manomono-23/e-otomo/firmware/e-otomo/qr_pattern.h

#ifndef QR_PATTERN_H
#define QR_PATTERN_H

// QR code pattern data (33x33 bits packed into bytes)
// Generated for "https://e-otomo.manomono.net/"
const uint8_t qr_pattern[] = {
  0x00, 0x00, 0x00, 0x00, 0x00, // Row  0: 000000000000000000000000000000000
  0x00, 0x00, 0x00, 0x00, 0x00, // Row  1: 000000000000000000000000000000000
  0x3F, 0xA1, 0xB8, 0xFE, 0x00, // Row  2: 001111111010000110111000111111100
  0x20, 0xA7, 0xD4, 0x82, 0x00, // Row  3: 001000001010011111010100100000100
  0x2E, 0xB2, 0x96, 0xBA, 0x00, // Row  4: 001011101011001010010110101110100
  0x2E, 0xBA, 0x0C, 0xBA, 0x00, // Row  5: 001011101011101000001100101110100
  0x2E, 0x9A, 0x18, 0xBA, 0x00, // Row  6: 001011101001101000011000101110100
  0x20, 0xB8, 0x34, 0x82, 0x00, // Row  7: 001000001011100000110100100000100
  0x3F, 0xAA, 0xAA, 0xFE, 0x00, // Row  8: 001111111010101010101010111111100
  0x00, 0x0D, 0x7A, 0x00, 0x00, // Row  9: 000000000000110101111010000000000
  0x33, 0x8B, 0x1A, 0x5E, 0x00, // Row 10: 001100111000101100011010010111100
  0x2A, 0x41, 0xB8, 0xFE, 0x00, // Row 11: 001010100100000110111000111111100
  0x20, 0xB8, 0x2A, 0x42, 0x00, // Row 12: 001000001011100000101010010000100
  0x1A, 0x72, 0x96, 0x16, 0x00, // Row 13: 000110100111001010010110000101100
  0x2F, 0xE5, 0xF3, 0x44, 0x00, // Row 14: 001011111110010111110011010001000
  0x23, 0x6A, 0x18, 0xFE, 0x00, // Row 15: 001000110110101000011000111111100
  0x0B, 0x8F, 0xC8, 0x3A, 0x00, // Row 16: 000010111000111111001000001110100
  0x3F, 0x3D, 0x76, 0xA6, 0x00, // Row 17: 001111110011110101110110101001100
  0x3E, 0xD3, 0x13, 0x04, 0x00, // Row 18: 001111101101001100010011000001000
  0x28, 0x29, 0xA8, 0xF6, 0x00, // Row 19: 001010000010100110101000111101100
  0x09, 0x88, 0x3A, 0x0A, 0x00, // Row 20: 000010011000100000111010000010100
  0x06, 0x1A, 0x98, 0x26, 0x00, // Row 21: 000001100001101010011000001001100
  0x3E, 0xFD, 0xF7, 0xF2, 0x00, // Row 22: 001111101111110111110111111100100
  0x00, 0x32, 0x06, 0x22, 0x00, // Row 23: 000000000011001000000110001000100
  0x3F, 0x8F, 0xDE, 0xBA, 0x00, // Row 24: 001111111000111111011110101110100
  0x20, 0xB5, 0x76, 0x22, 0x00, // Row 25: 001000001011010101110110001000100
  0x2E, 0xB3, 0x1F, 0xF6, 0x00, // Row 26: 001011101011001100011111111101100
  0x2E, 0x89, 0xBA, 0x04, 0x00, // Row 27: 001011101000100110111010000001000
  0x2E, 0x88, 0x2F, 0x5E, 0x00, // Row 28: 001011101000100000101111010111100
  0x20, 0xA2, 0x9A, 0x16, 0x00, // Row 29: 001000001010001010011010000101100
  0x3F, 0xB5, 0xCA, 0xF4, 0x00, // Row 30: 001111111011010111001010111101000
  0x00, 0x00, 0x00, 0x00, 0x00, // Row 31: 000000000000000000000000000000000
  0x00, 0x00, 0x00, 0x00, 0x00, // Row 32: 000000000000000000000000000000000
};

const uint8_t qr_size = 33;

#endif // QR_PATTERN_H
